sun9qd/electronics-with-bricks/Applications/MP3Player/README.md

# Electronics With Bricks

## MP3 Player

In this experiment an integrated MP3 player is used that provides a direct loudspeaker output. The circuit is limited to controlling this component using a series of buttons and connecting a miniature loudspeaker.

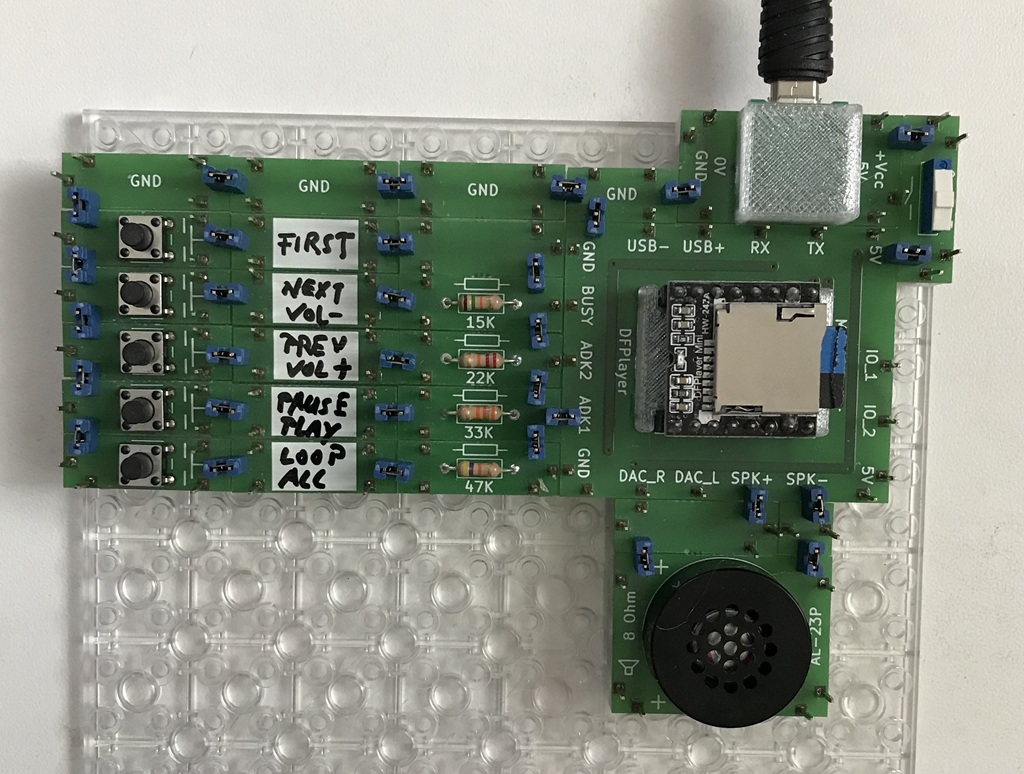
[picture p66: Applications/MP3Player/img/MP3Player.jpg]
MP3 Player


Copyright (c) 2024-2026 sun9qd
