sun9qd/electronics-with-bricks/Applications/Voltmeter/README.md

# Electronics With Bricks

## Voltmeter

In this experiment we build a voltmeter to measure electrical voltages.

The voltage is measured with an ADC (analog-digital converter) that is built into the D1-Mini microcontroller board.

The measured voltage is displayed on a small graphic display that is connected to the microcontroller via i2c.

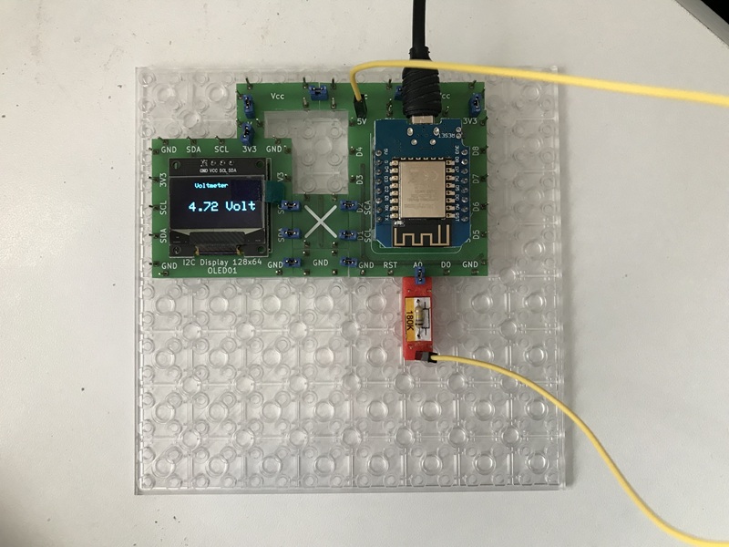
[picture p70: Applications/Voltmeter/img/Voltmeter.jpg]
Voltmeter


Copyright (c) 2024-2026 sun9qd
