sun9qd/electronics-with-bricks/Applications/TryIt/img/IMG_3256.JPG

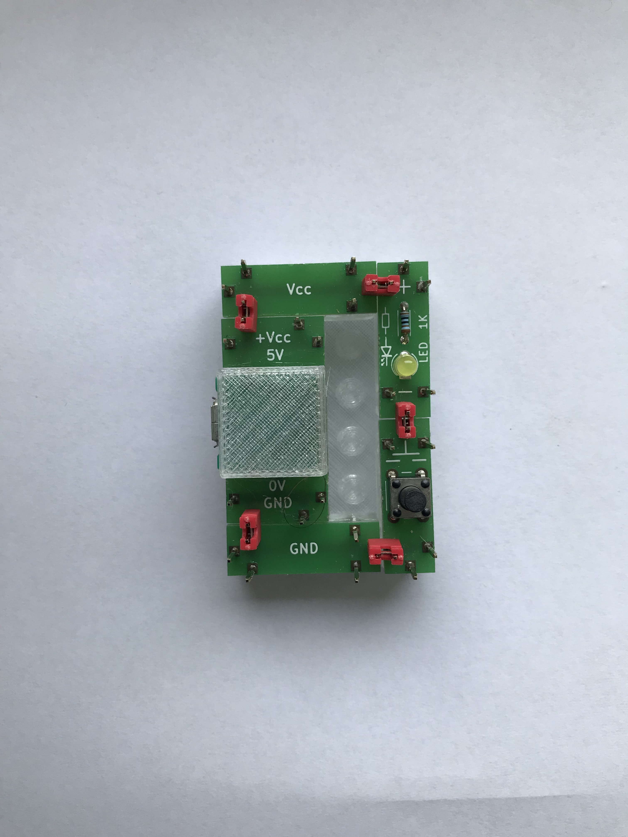
Applications/TryIt/img/IMG_3256.JPG
