sun9qd/electronics-with-bricks/Bricks/img/Brick_2x1_Connector_PinHeader.jpg

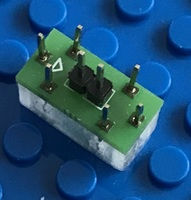
Bricks/img/Brick_2x1_Connector_PinHeader.jpg
