sun9qd/electronics-with-bricks/Bricks/img/Brick_3x1_Connector_PinHeader.jpg

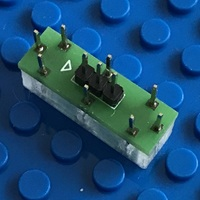
Bricks/img/Brick_3x1_Connector_PinHeader.jpg
