sun9qd/electronics-with-bricks/Bricks/img/Brick_3x1_Line.jpg

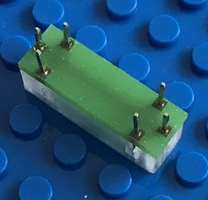
Bricks/img/Brick_3x1_Line.jpg
