sun9qd/electronics-with-bricks/Bricks/img/Brick_6x1_Connector_PinHeader.jpg

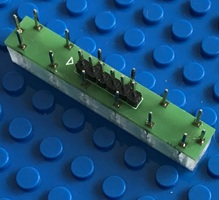
Bricks/img/Brick_6x1_Connector_PinHeader.jpg
