sun9qd/electronics-with-bricks/Bricks/img/Brick_NoPictureAvailable.jpg

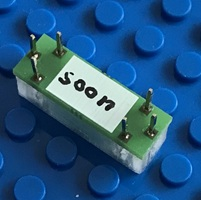
Bricks/img/Brick_NoPictureAvailable.jpg
