sun9qd/electronics-with-bricks/Resources/stl/body_3x2_fan.stl

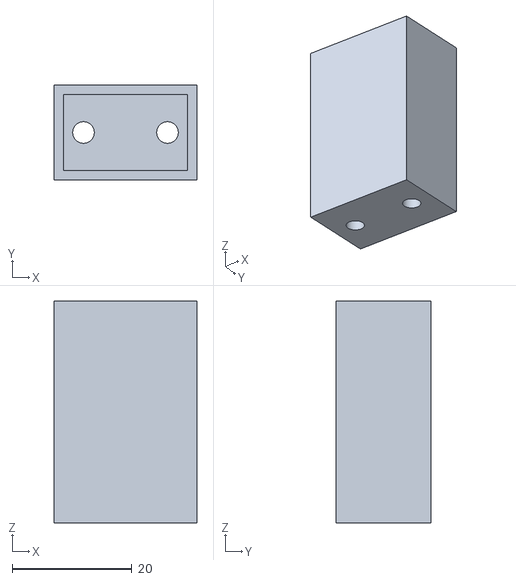
[picture p115: CAD file, 2026-10-09]
Resources/stl/body_3x2_fan.stl
23.8 x 15.8 x 37.0
