sun9qd/electronics-with-bricks/Resources/stl/body_4x1_solderingSupport.stl

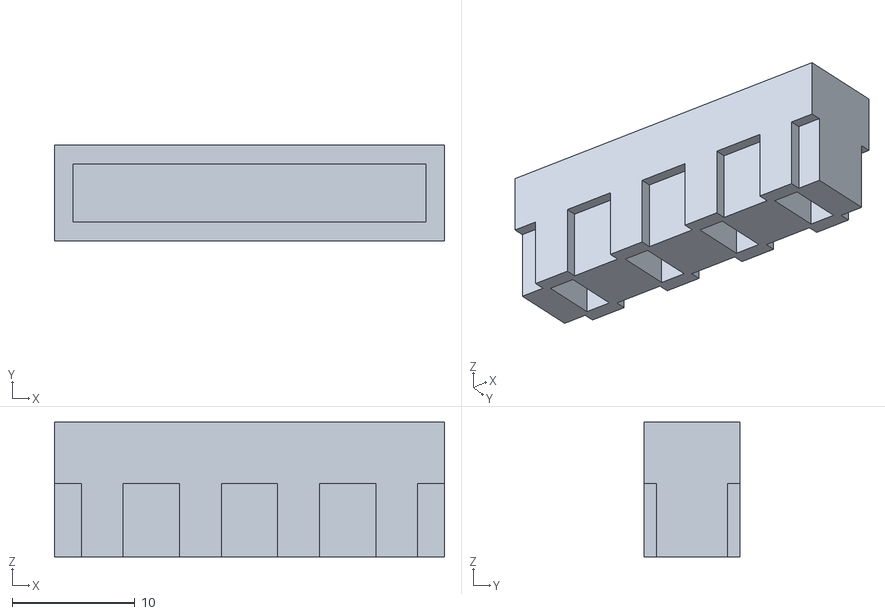
[picture p116: CAD file, 2026-10-09]
Resources/stl/body_4x1_solderingSupport.stl
31.8 x 7.80 x 11.0
