sun9qd/electronics-with-bricks/Resources/stl/body_7x3.stl

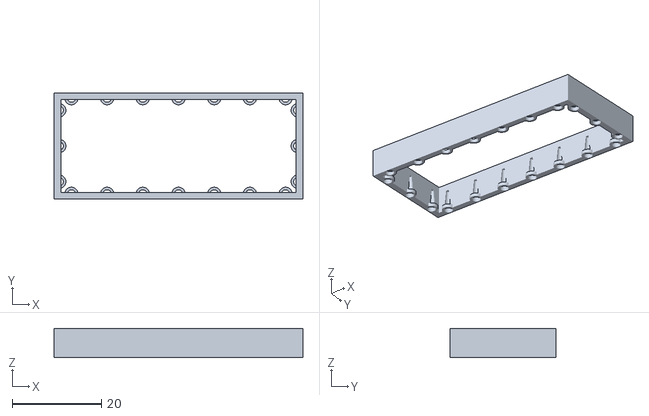
[picture p117: CAD file, 2026-10-09]
Resources/stl/body_7x3.stl
55.8 x 23.8 x 6.60
