sun9qd/electronics-with-bricks/Resources/stl/body_9x3.stl

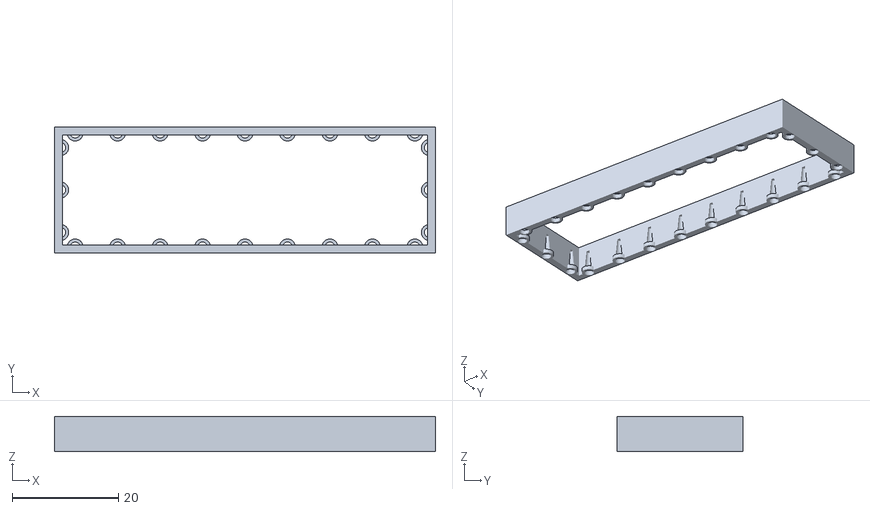
[picture p119: CAD file, 2026-10-09]
Resources/stl/body_9x3.stl
71.8 x 23.8 x 6.60
