sun9qd/electronics-with-bricks/Resources/stl/body_pushbutton_top.stl

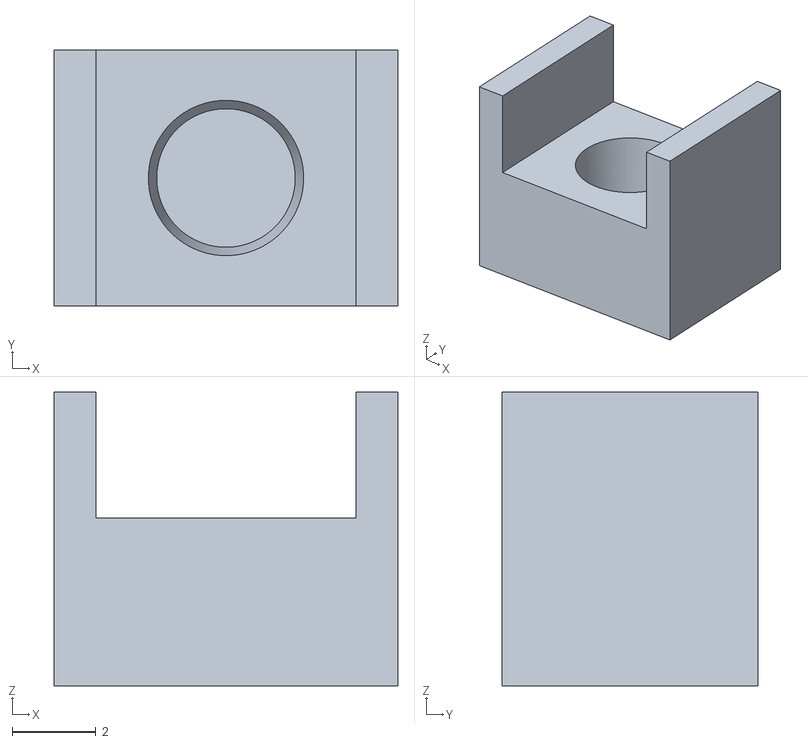
[picture p120: CAD file, 2026-10-09]
Resources/stl/body_pushbutton_top.stl
8.20 x 6.10 x 7.00
