sun9qd/electronics-with-bricks/Resources/stl/body_4x1.stl

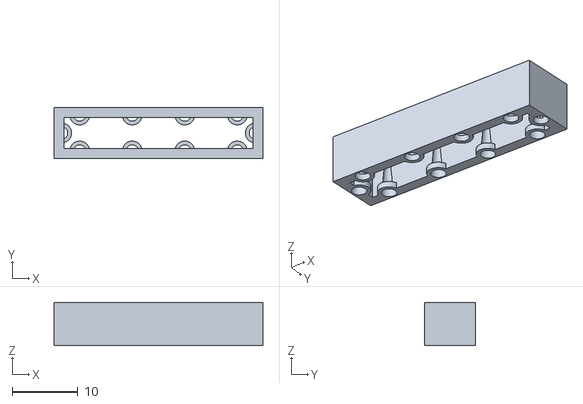
[picture p121: CAD file, 2026-10-09]
Resources/stl/body_4x1.stl
31.8 x 7.80 x 6.60
