sun9qd/electronics-with-bricks/Resources/stl/body_DFPlayer_top.stl

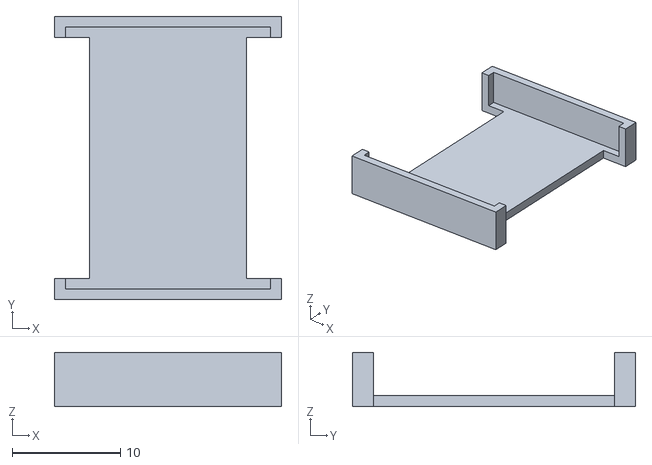
[picture p123: CAD file, 2026-10-09]
Resources/stl/body_DFPlayer_top.stl
21.0 x 26.2 x 5.00
