sun9qd/electronics-with-bricks/Resources/stl/body_8x8.stl

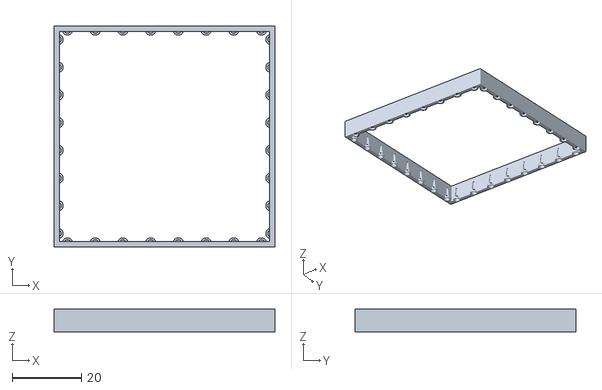
[picture p124: CAD file, 2026-10-09]
Resources/stl/body_8x8.stl
63.8 x 63.8 x 6.60
