sun9qd/electronics-with-bricks/Resources/stl/body_6x4_GroundPlate.stl

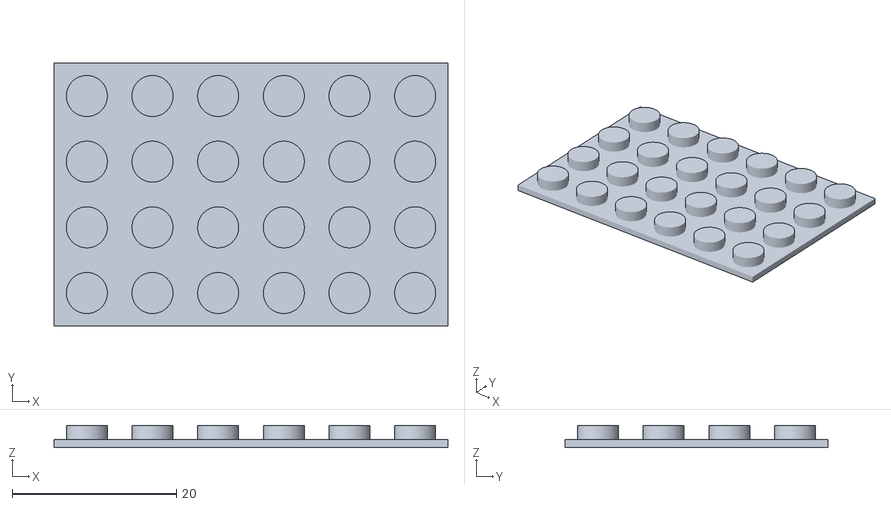
[picture p125: CAD file, 2026-10-09]
Resources/stl/body_6x4_GroundPlate.stl
48.0 x 32.0 x 2.70
