sun9qd/electronics-with-bricks/Resources/stl/body_4x4.stl

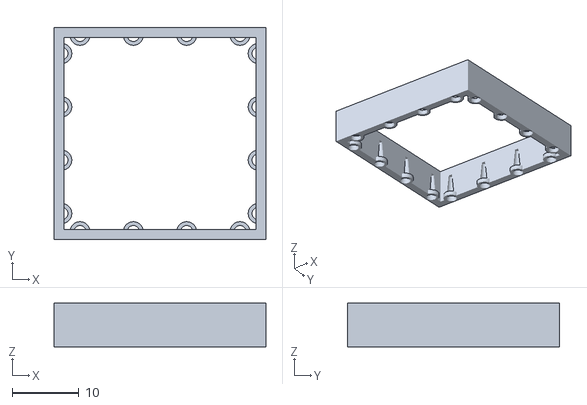
[picture p126: CAD file, 2026-10-09]
Resources/stl/body_4x4.stl
31.8 x 31.8 x 6.60
