sun9qd/electronics-with-bricks/Resources/stl/body_2x1.stl

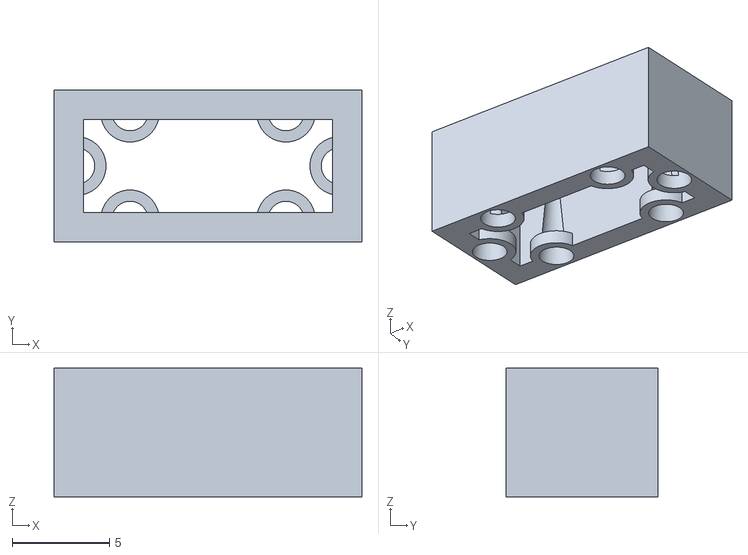
[picture p127: CAD file, 2026-10-09]
Resources/stl/body_2x1.stl
15.8 x 7.80 x 6.60
