sun9qd/electronics-with-bricks/Resources/stl/body_speakerBox_front.stl

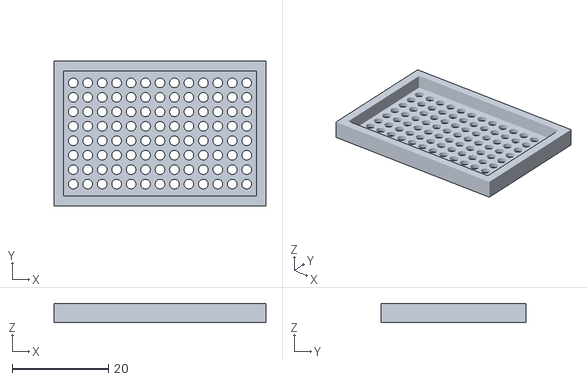
[picture p128: CAD file, 2026-10-09]
Resources/stl/body_speakerBox_front.stl
44.0 x 30.0 x 4.00
