sun9qd/electronics-with-bricks/Resources/stl/body_4x3.stl

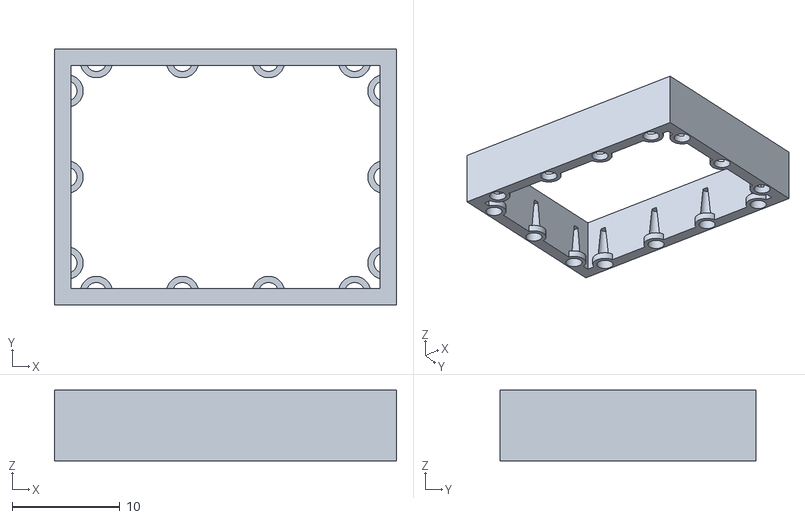
[picture p129: CAD file, 2026-10-09]
Resources/stl/body_4x3.stl
31.8 x 23.8 x 6.60
