sun9qd/electronics-with-bricks/Resources/stl/body_Voltmeter_top.stl

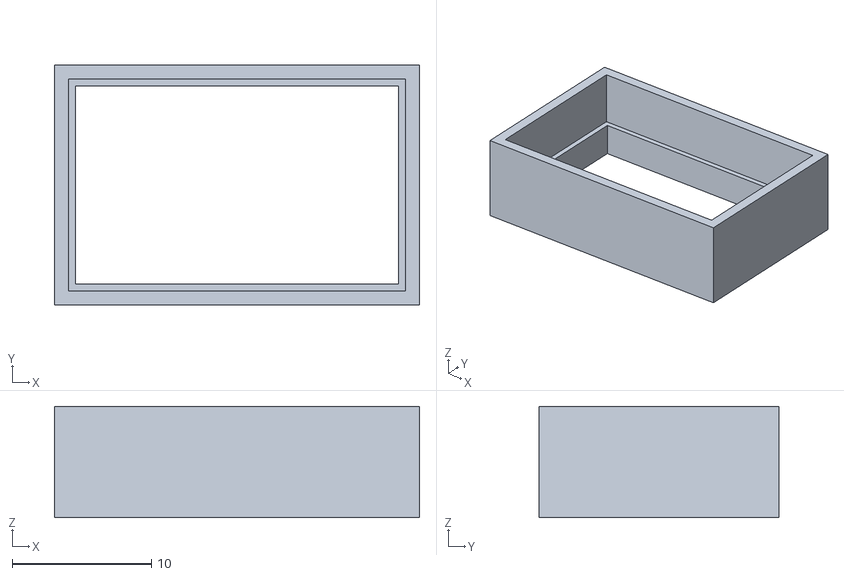
[picture p130: CAD file, 2026-10-09]
Resources/stl/body_Voltmeter_top.stl
26.2 x 17.2 x 8.00
