sun9qd/electronics-with-bricks/Resources/stl/body_microUSB_top.stl

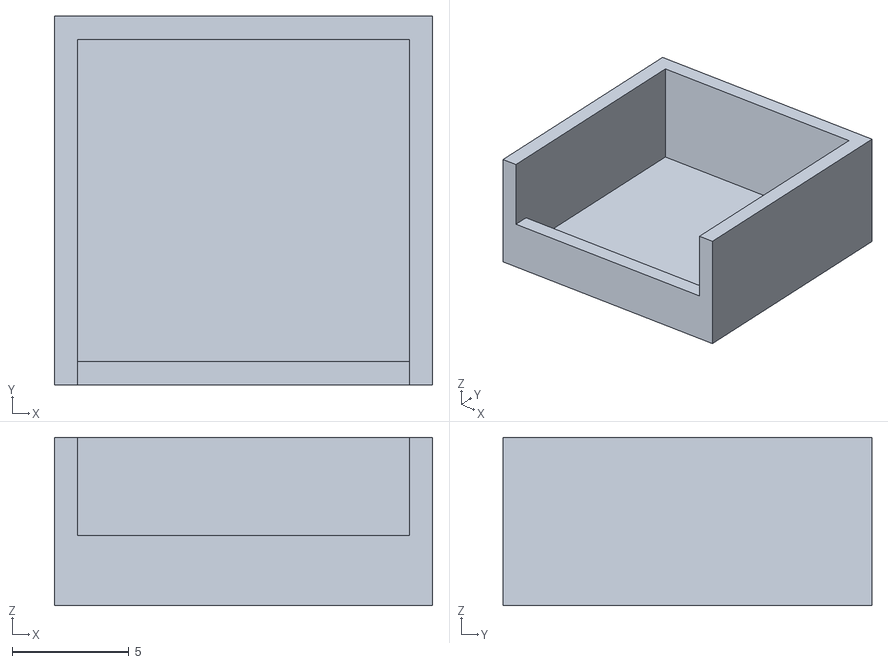
[picture p131: CAD file, 2026-10-09]
Resources/stl/body_microUSB_top.stl
16.2 x 15.8 x 7.20
