sun9qd/electronics-with-bricks/Resources/stl/body_2x2.stl

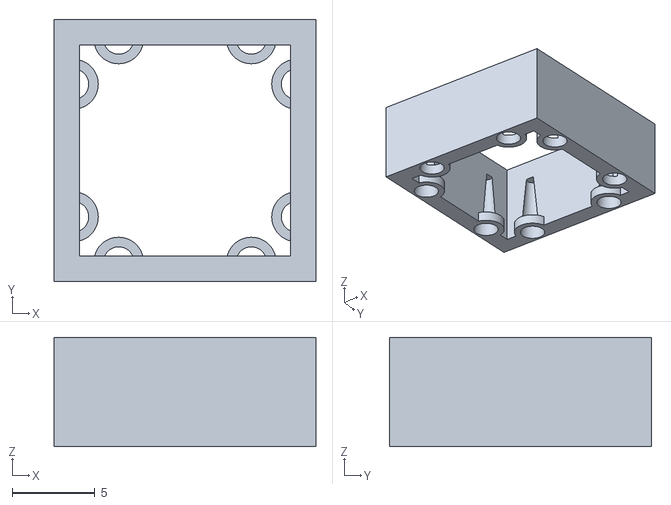
[picture p134: CAD file, 2026-10-09]
Resources/stl/body_2x2.stl
15.8 x 15.8 x 6.60
