sun9qd/electronics-with-bricks/Resources/stl/body_CableMarker.stl

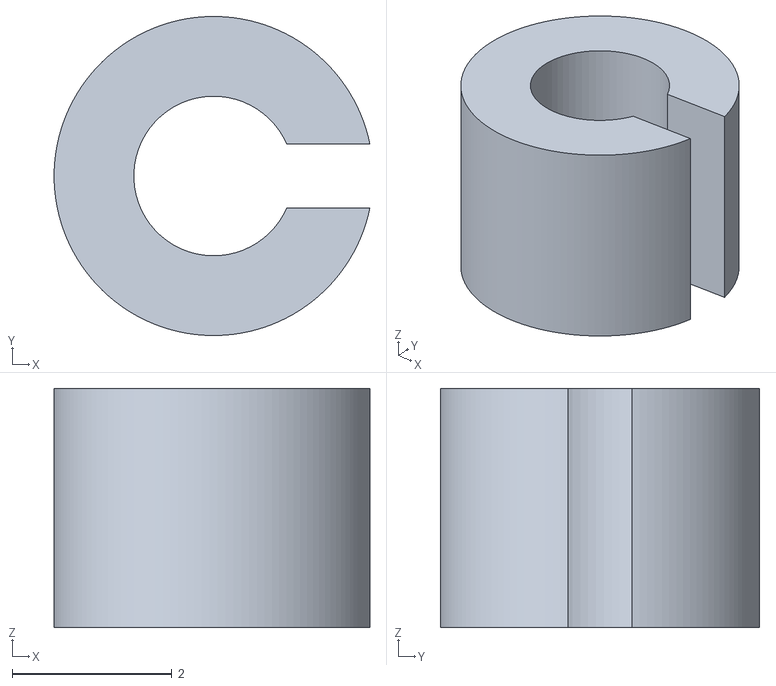
[picture p135: CAD file, 2026-10-09]
Resources/stl/body_CableMarker.stl
3.96 x 4.00 x 3.00
